dhanuzch/Assam_hackathon/2_Tracker for Forest road/Code/img/car3.jpg

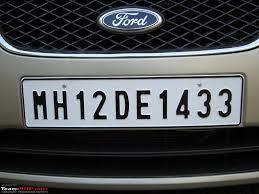
2_Tracker for Forest road/Code/img/car3.jpg
