dhanuzch/Assam_hackathon/Project_Images/1_device_LCD_not_in_motion.jpg

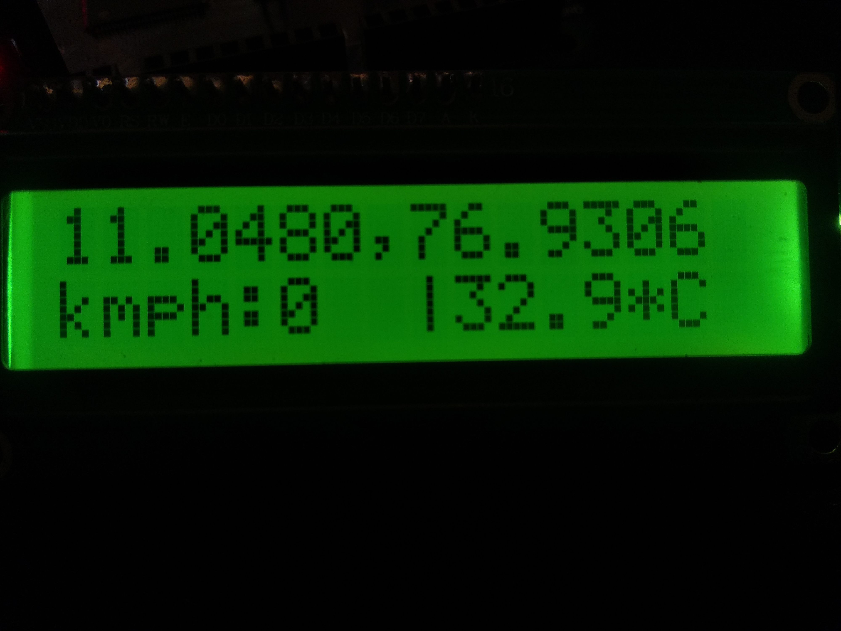
Project_Images/1_device_LCD_not_in_motion.jpg
