dhanuzch/Assam_hackathon/Project_Images/1_PCBBoard.png

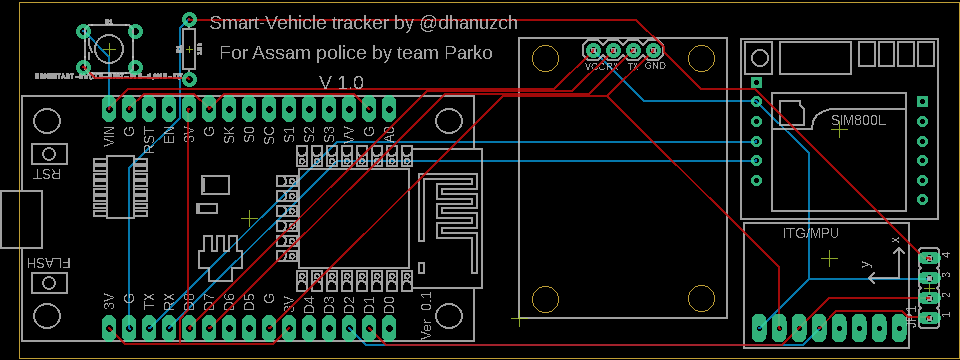
Project_Images/1_PCBBoard.png
