dhanuzch/Assam_hackathon/Project_Images/1_website.gif

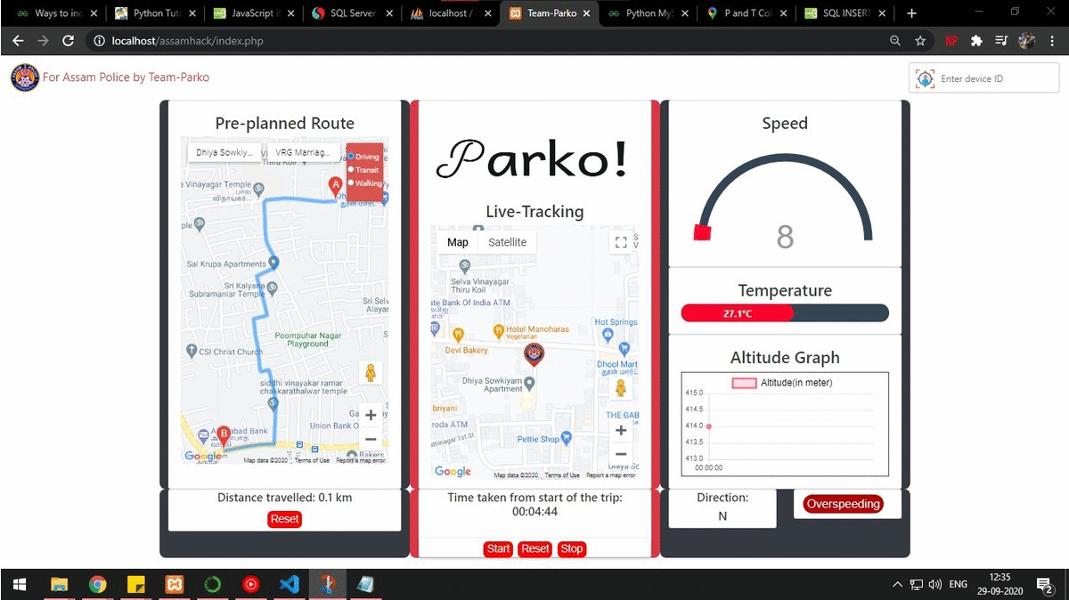
Project_Images/1_website.gif
