dhanuzch/Assam_hackathon/Project_Images/1_website_desktop.jpg

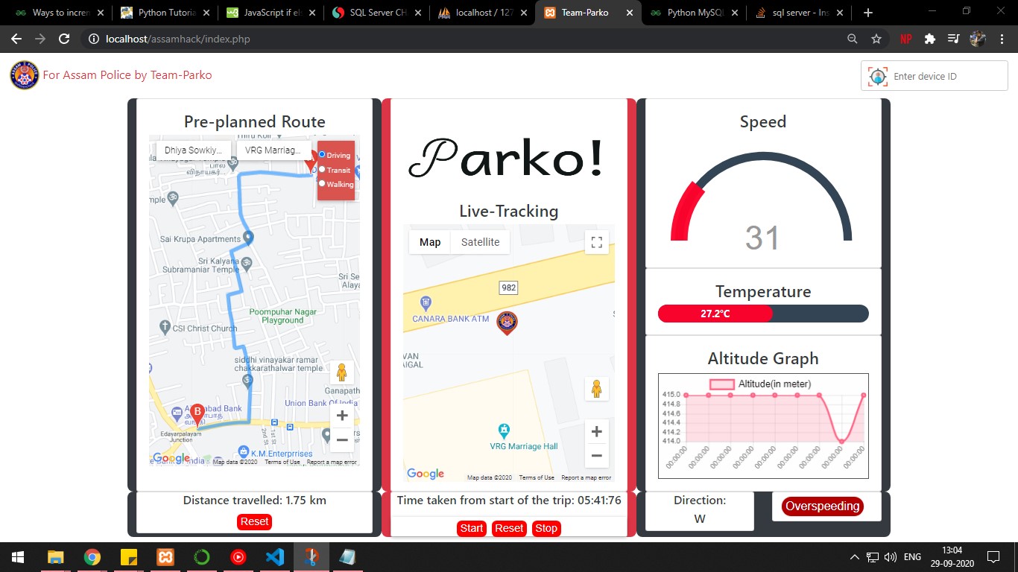
Project_Images/1_website_desktop.jpg
