dhanuzch/Assam_hackathon/Project_Images/1_website_mobile2.jpg

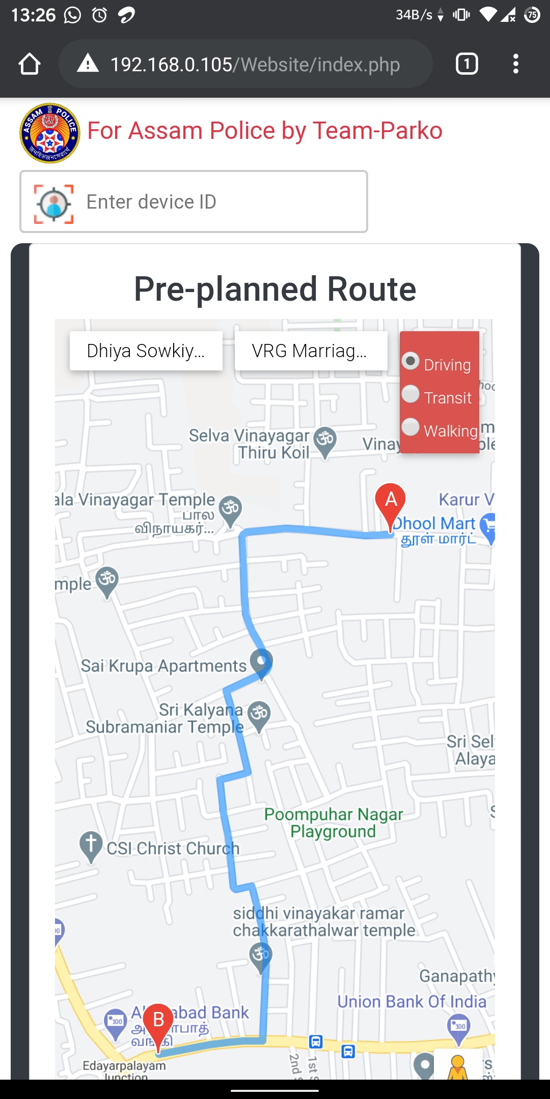
Project_Images/1_website_mobile2.jpg
