dhanuzch/Assam_hackathon/Project_Images/1_website_mobile.jpg

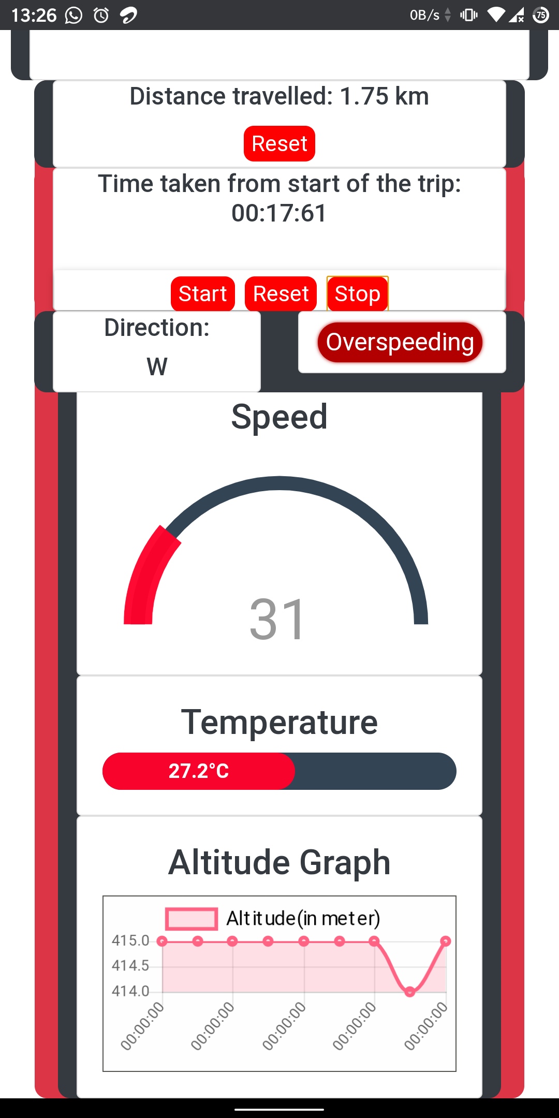
Project_Images/1_website_mobile.jpg
