dhanuzch/Assam_hackathon/Project_Images/1_website_speedalert.jpg

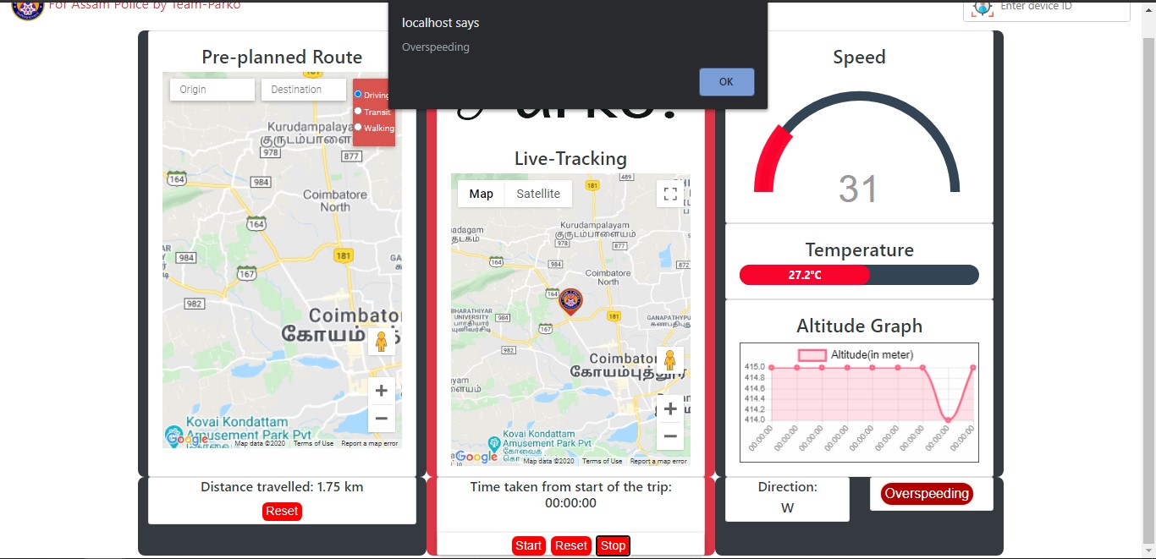
Project_Images/1_website_speedalert.jpg
