dhanuzch/Assam_hackathon/Project_Images/2_website.jpg

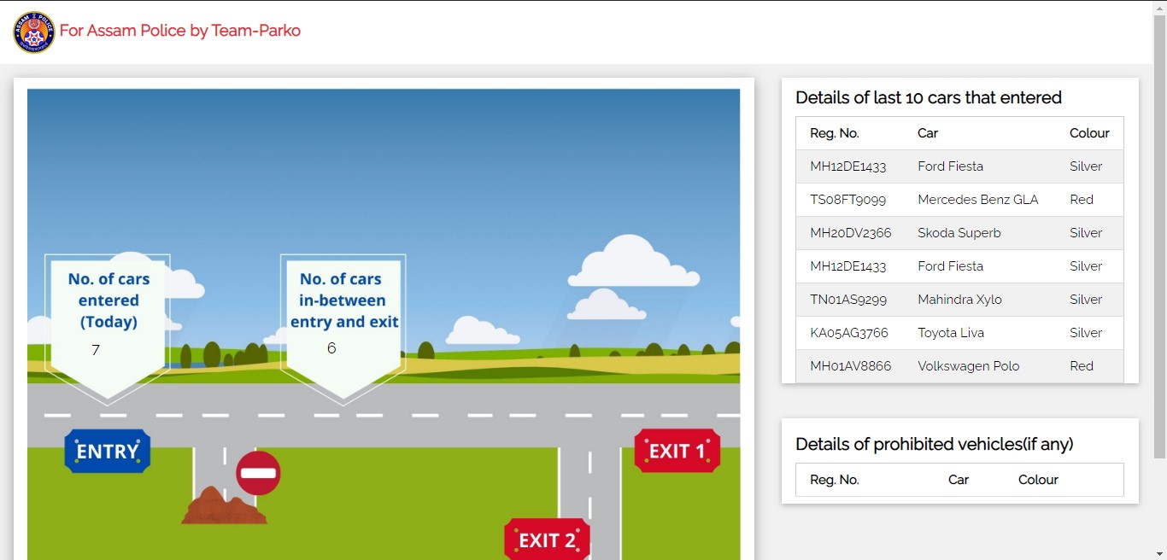
Project_Images/2_website.jpg
