dhanuzch/Assam_hackathon/Project_Images/2_websitealert.jpg

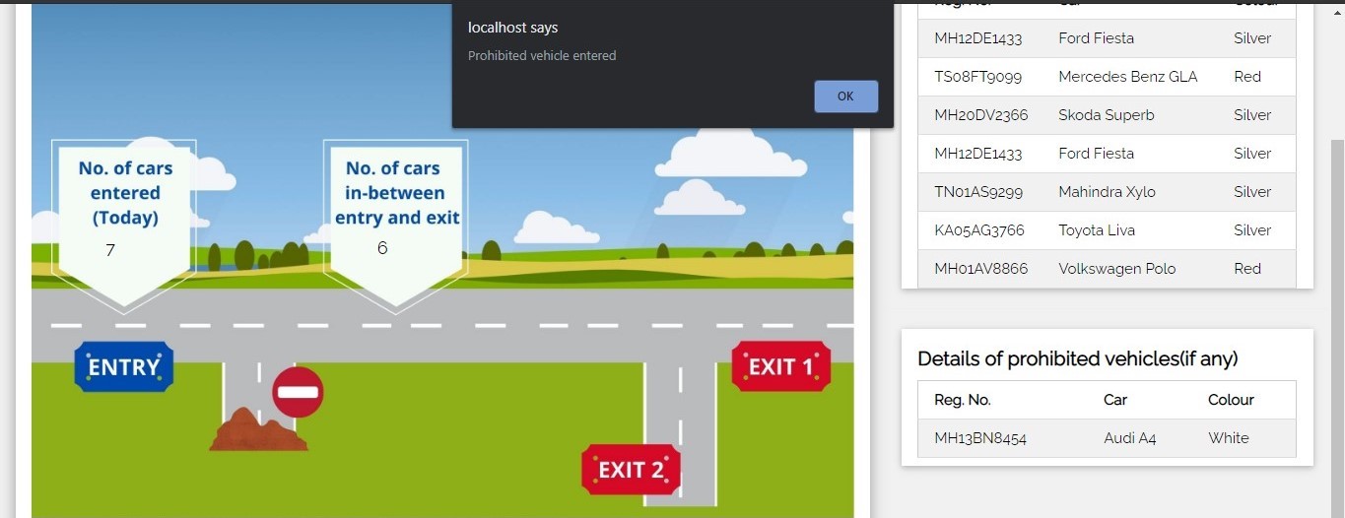
Project_Images/2_websitealert.jpg
